shmoergh/hog/boards/ui/sheets/adsr-logic.kicad_sch

## KiCad design boards/ui/sheets/adsr-logic.kicad_sch (2025-03-16)

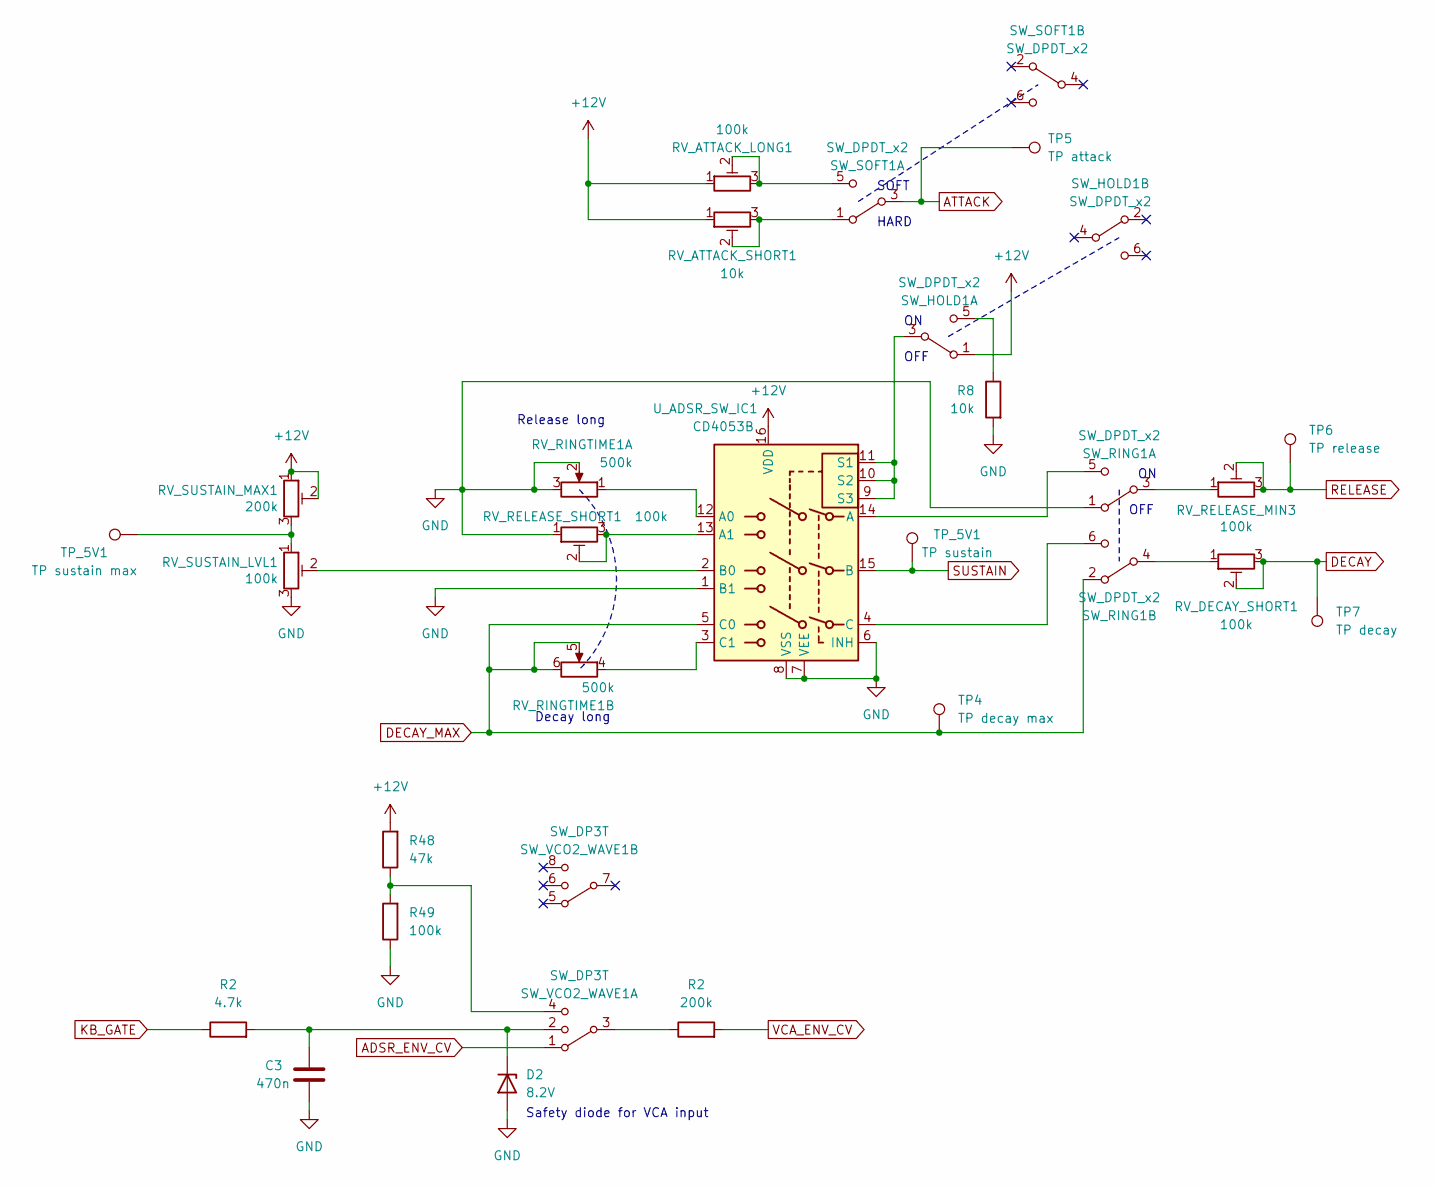
[picture p43: schematic adsr-logic.kicad_sch]

Parts:
C3: 470n; C_Disc_D3.0mm_W2.0mm_P2.50mm; Part No. 80-C315C474K5R
D2: 8.2V; D_DO-41_SOD81_P7.62mm_Horizontal; Part No. 625-BZX85C8V2
R2: 200k; R_Axial_DIN0207_L6.3mm_D2.5mm_P7.62mm_Horizontal; Part No. 603-MFR-25FTF52-200K
R8: 10k; R_Axial_DIN0207_L6.3mm_D2.5mm_P7.62mm_Horizontal; Part No. 603-MFR25SFRF52-10K
R48: 47k; R_Axial_DIN0207_L6.3mm_D2.5mm_P7.62mm_Horizontal; Part No. 603-MFR-25FTE52-47K
R49: 100k; R_Axial_DIN0207_L6.3mm_D2.5mm_P7.62mm_Horizontal; Part No. 603-MFR-25FRF52100K
RV_ATTACK_LONG1: 100k; Potentiometer_Runtron_RM-065_Vertical; Part No. 652-3306F-1-104
RV_ATTACK_SHORT1: 10k; Potentiometer_Runtron_RM-065_Vertical; Part No. 652-3306F-1-103
RV_DECAY_SHORT1: 100k; Potentiometer_Runtron_RM-065_Vertical; Part No. 652-3306F-1-104
RV_RELEASE_MIN3: 100k; Potentiometer_Runtron_RM-065_Vertical; Part No. 652-3306F-1-104
RV_RELEASE_SHORT1: 100k; Potentiometer_Runtron_RM-065_Vertical; Part No. 652-3306F-1-104
RV_RINGTIME1: 500k; Potentiometer_Bourns_Dual-PTV112-4; Part No. 652-PTV1124420AA504
RV_SUSTAIN_LVL1: 100k; Potentiometer_Runtron_RM-065_Vertical; Part No. 652-3306F-1-104
RV_SUSTAIN_MAX1: 200k; Potentiometer_Runtron_RM-065_Vertical; Part No. 652-3306F-1-204
SW_HOLD1: SW_DPDT_x2; DPDT Korg Style Switch; Part No. TS-22E01AT15
SW_RING1: SW_DPDT_x2; DPDT Korg Style Switch; Part No. TS-22E01AT15
SW_SOFT1: SW_DPDT_x2; DPDT Korg Style Switch; Part No. TS-22E01AT15
SW_VCO2_WAVE1: SW_DP3T; DP3T Korg Style Switch; Part No. TS23-E02
TP4: TP decay max; TestPoint_THTPad_2.0x2.0mm_Drill1.0mm
TP5: TP attack; TestPoint_THTPad_2.0x2.0mm_Drill1.0mm
TP6: TP release; TestPoint_THTPad_2.0x2.0mm_Drill1.0mm
TP7: TP decay; TestPoint_THTPad_2.0x2.0mm_Drill1.0mm
TP_5V1: TP sustain; TestPoint_THTPad_2.0x2.0mm_Drill1.0mm
U_ADSR_SW_IC1: CD4053B; DIP-16_W7.62mm; Part No. 595-CD4053BE

Connections:
+12V: R48.2, RV_ATTACK_LONG1.1, RV_ATTACK_SHORT1.1, RV_SUSTAIN_MAX1.1, RV_SUSTAIN_MAX1.2, SW_HOLD1.1 (A), U_ADSR_SW_IC1.16 (VDD)
ADSR_ENV_CV: SW_VCO2_WAVE1.1
ATTACK: SW_SOFT1.3 (B), TP5.1
DECAY: RV_DECAY_SHORT1.2, RV_DECAY_SHORT1.3, TP7.1
DECAY_MAX: RV_RINGTIME1.5, RV_RINGTIME1.6, SW_RING1.2 (A), TP4.1, U_ADSR_SW_IC1.5 (C0)
GND: C3.2, D2.2 (A), R8.2, R49.1, RV_RELEASE_SHORT1.1, RV_RINGTIME1.2, RV_RINGTIME1.3, RV_SUSTAIN_LVL1.3, SW_RING1.1 (A), U_ADSR_SW_IC1.1 (B1), U_ADSR_SW_IC1.6 (INH), U_ADSR_SW_IC1.7 (VEE), U_ADSR_SW_IC1.8 (VSS)
KB_GATE: R2.1
unnamed: C3.1, D2.1 (K), R2.2, SW_VCO2_WAVE1.2
unnamed: R2.1, SW_VCO2_WAVE1.3
unnamed: R8.1, SW_HOLD1.5 (C)
unnamed: R48.1, R49.2, SW_VCO2_WAVE1.4
unnamed: RV_ATTACK_LONG1.2, RV_ATTACK_LONG1.3, SW_SOFT1.5 (C)
unnamed: RV_ATTACK_SHORT1.2, RV_ATTACK_SHORT1.3, SW_SOFT1.1 (A)
unnamed: RV_DECAY_SHORT1.1, SW_RING1.4 (B)
unnamed: RV_RELEASE_MIN3.1, SW_RING1.3 (B)
unnamed: RV_RELEASE_SHORT1.2, RV_RELEASE_SHORT1.3, U_ADSR_SW_IC1.13 (A1)
unnamed: RV_RINGTIME1.1, U_ADSR_SW_IC1.12 (A0)
unnamed: RV_RINGTIME1.4, U_ADSR_SW_IC1.3 (C1)
unnamed: RV_SUSTAIN_LVL1.1, RV_SUSTAIN_MAX1.3, TP_5V1.1
unnamed: RV_SUSTAIN_LVL1.2, U_ADSR_SW_IC1.2 (B0)
unnamed: SW_HOLD1.3 (B), U_ADSR_SW_IC1.9 (S3), U_ADSR_SW_IC1.10 (S2), U_ADSR_SW_IC1.11 (S1)
unnamed: SW_RING1.5 (C), U_ADSR_SW_IC1.14 (A)
unnamed: SW_RING1.6 (C), U_ADSR_SW_IC1.4 (C)
RELEASE: RV_RELEASE_MIN3.2, RV_RELEASE_MIN3.3, TP6.1
SUSTAIN: TP_5V1.1, U_ADSR_SW_IC1.15 (B)
VCA_ENV_CV: R2.2

Notes on the sheet:
Release long
HARD
SOFT
OFF
Decay long
Safety diode for VCA input
