shmoergh/hog/boards/ui/sheets/filter_ui.kicad_sch

## KiCad design boards/ui/sheets/filter_ui.kicad_sch (2025-03-16)

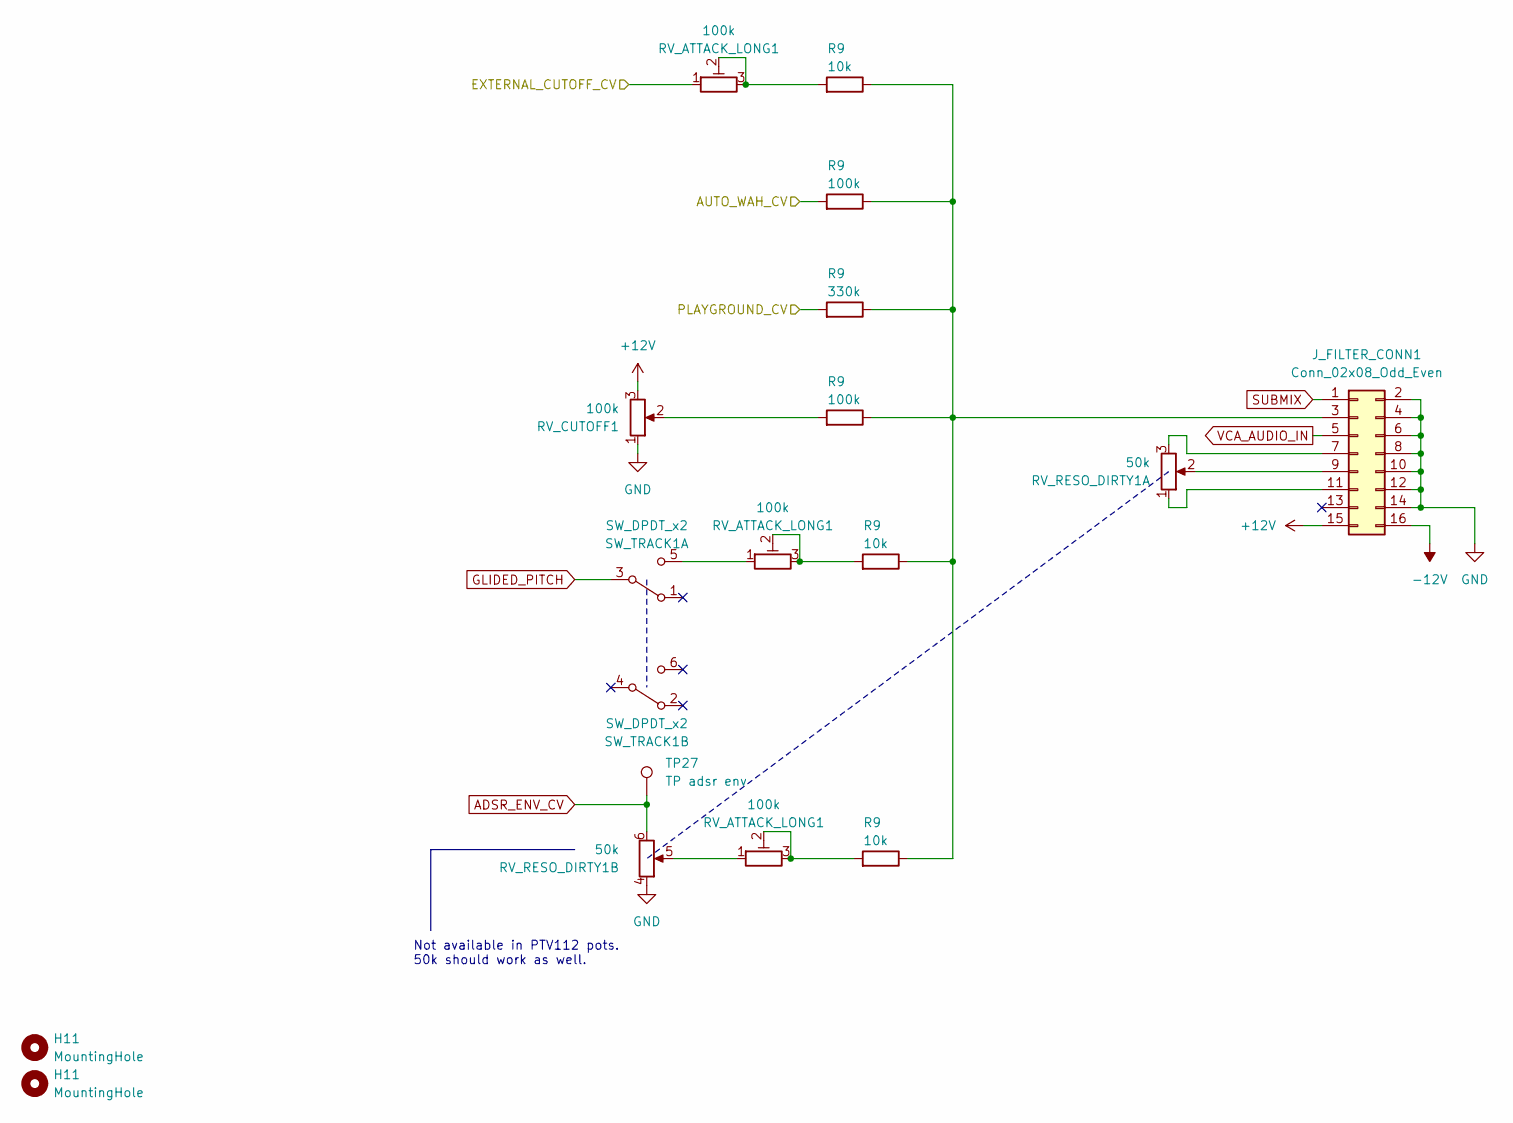
[picture p44: schematic filter_ui.kicad_sch]

Parts:
H11: MountingHole; MountingHole_3mm
J_FILTER_CONN1: Conn_02x08_Odd_Even; PinHeader_2x08_P2.54mm_Vertical; Part No. 649-1012938191601BLF
R9: 100k; R_Axial_DIN0207_L6.3mm_D2.5mm_P7.62mm_Horizontal; Part No. 603-MFR-25FRF52100K
RV_ATTACK_LONG1: 100k; Potentiometer_Runtron_RM-065_Vertical; Part No. 652-3306F-1-104
RV_CUTOFF1: 100k; Potentiometer_Bourns_Single-PTV09A; Part No. 652-PTV09A4025FB104
RV_RESO_DIRTY1: 50k; Potentiometer_Bourns_Dual-PTV112-4; Part No. 652-PTV112-4425AB503
SW_TRACK1: SW_DPDT_x2; DPDT Korg Style Switch; Part No. TS-22E01AT15
TP27: TP adsr env; TestPoint_THTPad_2.0x2.0mm_Drill1.0mm

Connections:
+12V: J_FILTER_CONN1.15, RV_CUTOFF1.3
-12V: J_FILTER_CONN1.16
ADSR_ENV_CV: RV_RESO_DIRTY1.6, TP27.1
AUTO_WAH_CV: R9.2
EXTERNAL_CUTOFF_CV: RV_ATTACK_LONG1.1
GLIDED_PITCH: SW_TRACK1.3 (B)
GND: J_FILTER_CONN1.2, J_FILTER_CONN1.4, J_FILTER_CONN1.6, J_FILTER_CONN1.8, J_FILTER_CONN1.10, J_FILTER_CONN1.12, J_FILTER_CONN1.14, RV_CUTOFF1.1, RV_RESO_DIRTY1.4
unnamed: J_FILTER_CONN1.3, R9.1
unnamed: J_FILTER_CONN1.7, RV_RESO_DIRTY1.3
unnamed: J_FILTER_CONN1.9, RV_RESO_DIRTY1.2
unnamed: J_FILTER_CONN1.11, RV_RESO_DIRTY1.1
unnamed: R9.2, RV_ATTACK_LONG1.2, RV_ATTACK_LONG1.3, RV_CUTOFF1.2
unnamed: RV_ATTACK_LONG1.1, RV_RESO_DIRTY1.5, SW_TRACK1.5 (C)
PLAYGROUND_CV: R9.2
SUBMIX: J_FILTER_CONN1.1
VCA_AUDIO_IN: J_FILTER_CONN1.5

Notes on the sheet:
Not available in PTV112 pots. 50k should work as well.
