shmoergh/hog/boards/ui/sheets/glide_ui.kicad_sch

## KiCad design boards/ui/sheets/glide_ui.kicad_sch (2024-12-14)

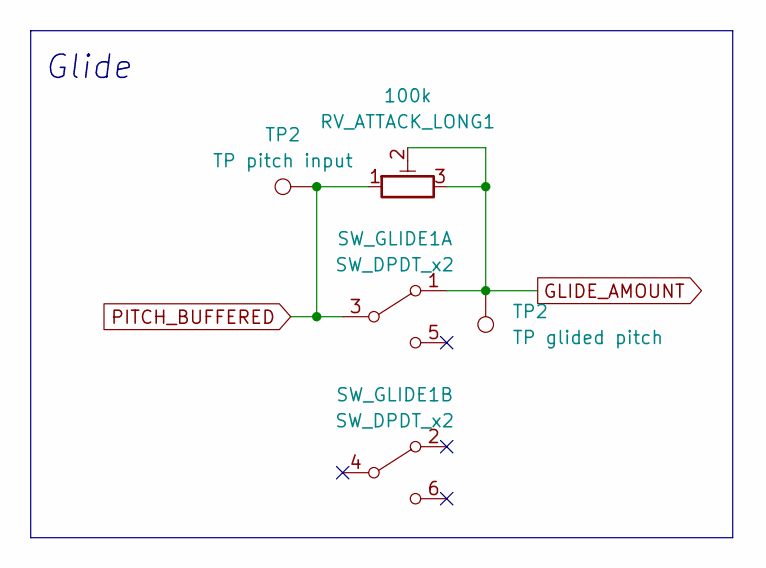
[picture p45: schematic glide_ui.kicad_sch]

Parts:
RV_ATTACK_LONG1: 100k; Potentiometer_Runtron_RM-065_Vertical; Part No. 652-3306F-1-104
SW_GLIDE1: SW_DPDT_x2; DPDT Korg Style Switch; Part No. TS-22E01AT15
TP2: TP glided pitch; TestPoint_THTPad_2.0x2.0mm_Drill1.0mm

Connections:
GLIDE_AMOUNT: RV_ATTACK_LONG1.2, RV_ATTACK_LONG1.3, SW_GLIDE1.1 (A), TP2.1
PITCH_BUFFERED: RV_ATTACK_LONG1.1, SW_GLIDE1.3 (B), TP2.1

Notes on the sheet:
Glide
