shmoergh/hog/boards/ui/sheets/io.kicad_sch

## KiCad design boards/ui/sheets/io.kicad_sch (2025-03-16)

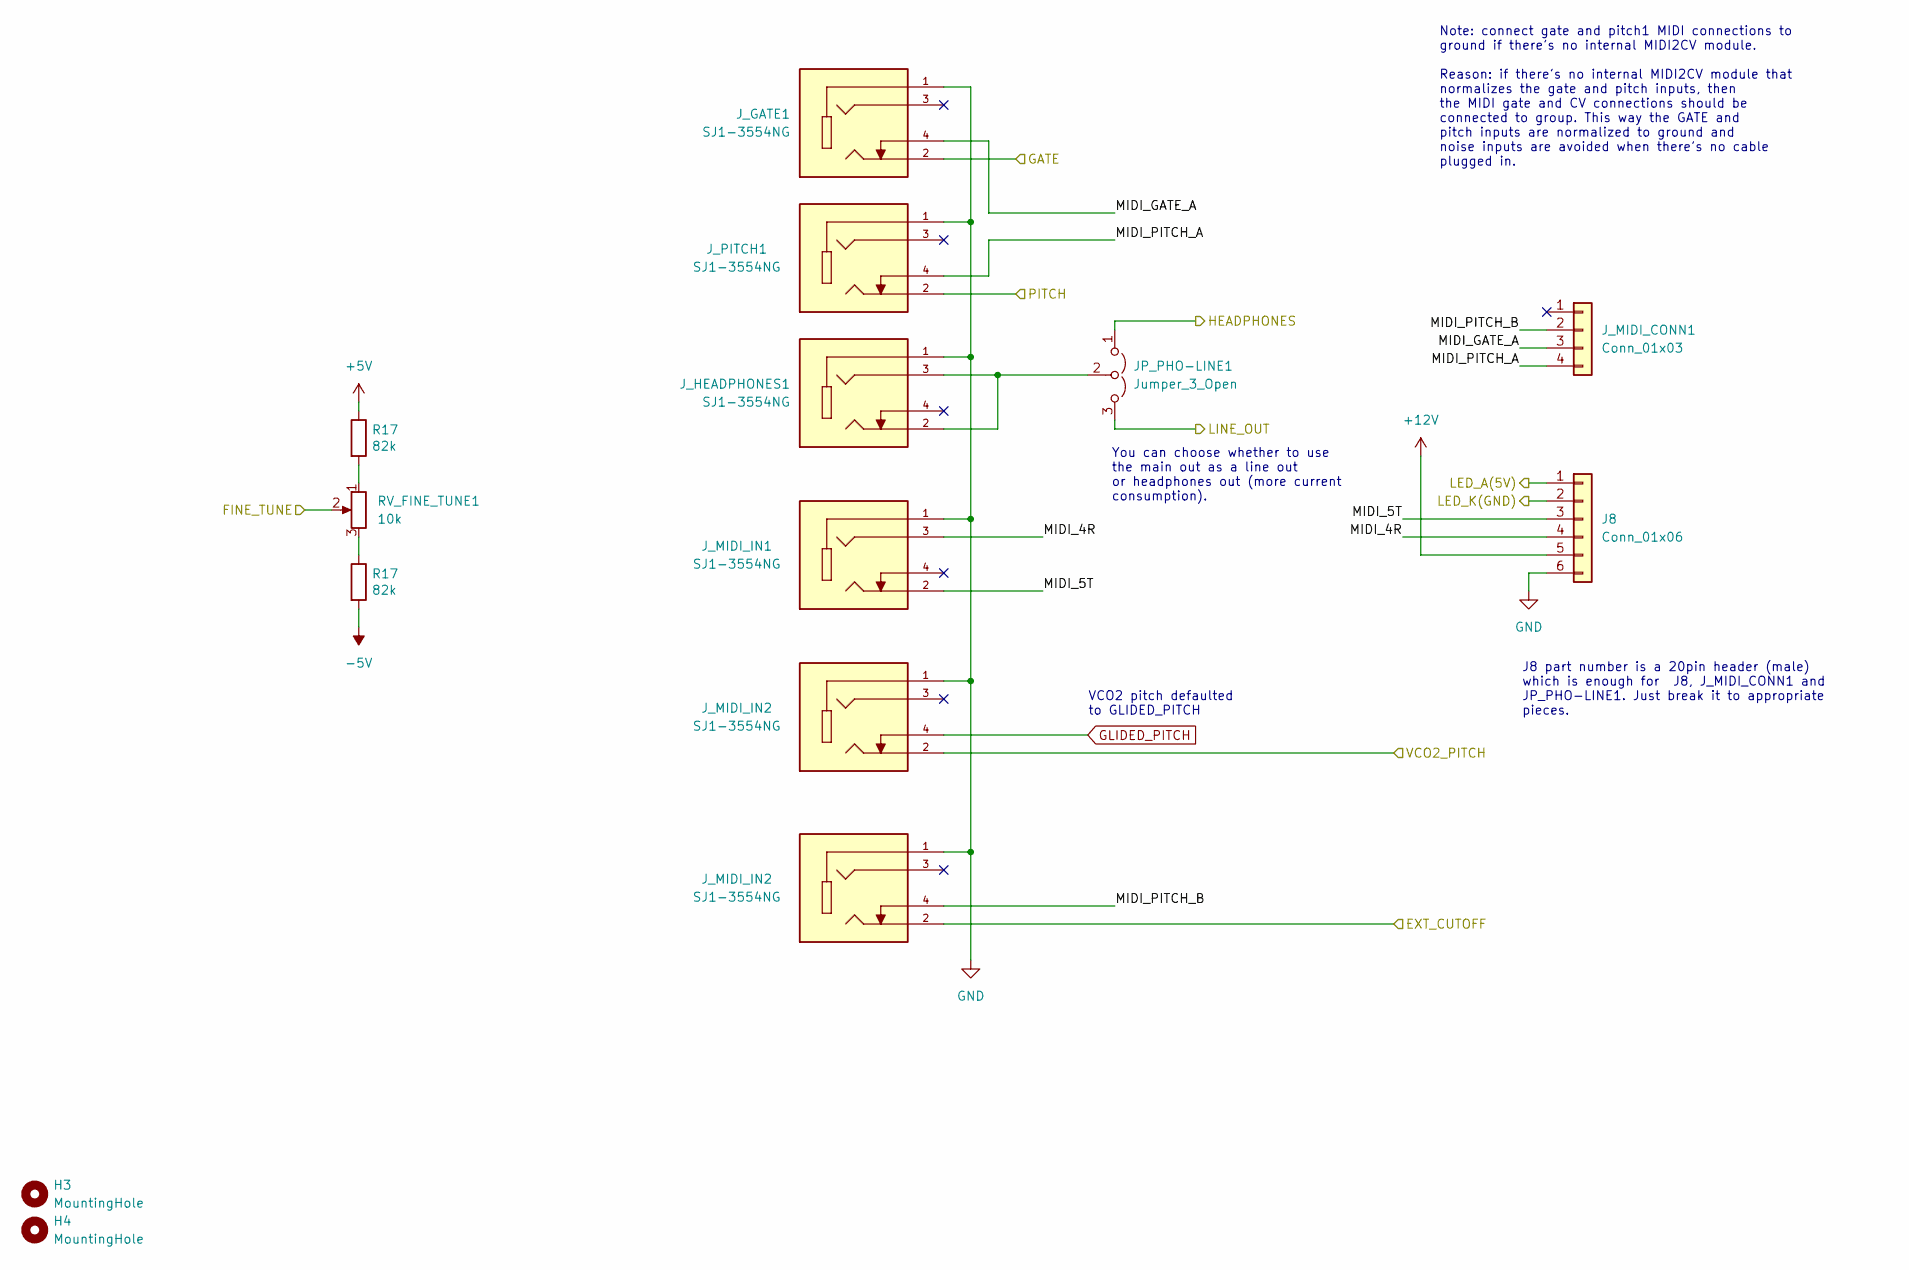
[picture p46: schematic io.kicad_sch]

Parts:
H3, H4: MountingHole; MountingHole_3mm_Pad
J8: Conn_01x06; PinHeader_1x06_P2.54mm_Vertical; Part No. 737-PH1-20-UA
JP_PHO-LINE1: Jumper_3_Open; PinHeader_1x03_P2.54mm_Vertical
J_GATE1: SJ1-3554NG; CUI_SJ1-3554NG; PARTREV 1.05
J_HEADPHONES1: SJ1-3554NG; CUI_SJ1-3554NG; PARTREV 1.05
J_MIDI_CONN1: Conn_01x03; PinHeader_1x04_P2.54mm_Vertical
J_MIDI_IN1, J_MIDI_IN2: SJ1-3554NG; CUI_SJ1-3554NG; PARTREV 1.05
J_PITCH1: SJ1-3554NG; CUI_SJ1-3554NG; PARTREV 1.05
R17: 82k; R_Axial_DIN0207_L6.3mm_D2.5mm_P7.62mm_Horizontal; Part No. 603-MFR-25FBF52-82K
RV_FINE_TUNE1: 10k; Potentiometer_Bourns_PTD901-2015_Single_Horizontal; Part No. PTD901-1015K-B103

Connections:
+5V: R17.1
+12V: J8.5
-5V: R17.2
EXT_CUTOFF: J_MIDI_IN2.2
FINE_TUNE: RV_FINE_TUNE1.2
GATE: J_GATE1.2
GLIDED_PITCH: J_MIDI_IN2.4
GND: J8.6, J_GATE1.1, J_HEADPHONES1.1, J_MIDI_IN1.1, J_MIDI_IN2.1, J_PITCH1.1
HEADPHONES: JP_PHO-LINE1.1 (A)
LED_A(5V): J8.1
LED_K(GND): J8.2
LINE_OUT: JP_PHO-LINE1.3 (B)
MIDI_4R: J8.4, J_MIDI_IN1.3
MIDI_5T: J8.3, J_MIDI_IN1.2
MIDI_GATE_A: J_GATE1.4, J_MIDI_CONN1.3
MIDI_PITCH_A: J_MIDI_CONN1.4, J_PITCH1.4
MIDI_PITCH_B: J_MIDI_CONN1.2, J_MIDI_IN2.4
unnamed: JP_PHO-LINE1.2 (C), J_HEADPHONES1.2, J_HEADPHONES1.3
unnamed: R17.1, RV_FINE_TUNE1.3
unnamed: R17.2, RV_FINE_TUNE1.1
PITCH: J_PITCH1.2
VCO2_PITCH: J_MIDI_IN2.2

Notes on the sheet:
You can choose whether to use the main out as a line out or headphones out (more current consumption).
VCO2 pitch defaulted to GLIDED_PITCH
J8 part number is a 20pin header (male) which is enough for J8, J_MIDI_CONN1 and JP_PHO-LINE1. Just break it to appropriate pieces.
Note: connect gate and pitch1 MIDI connections to ground if there's no internal MIDI2CV module. Reason: if there's no internal MIDI2CV module that normalizes the gate and pitch inputs, then the MIDI gate and CV connections should be connected to group. This way the GATE and pitch inputs are normali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
