shmoergh/hog/boards/ui/sheets/lfo_ui.kicad_sch

## KiCad design boards/ui/sheets/lfo_ui.kicad_sch (2025-03-16)

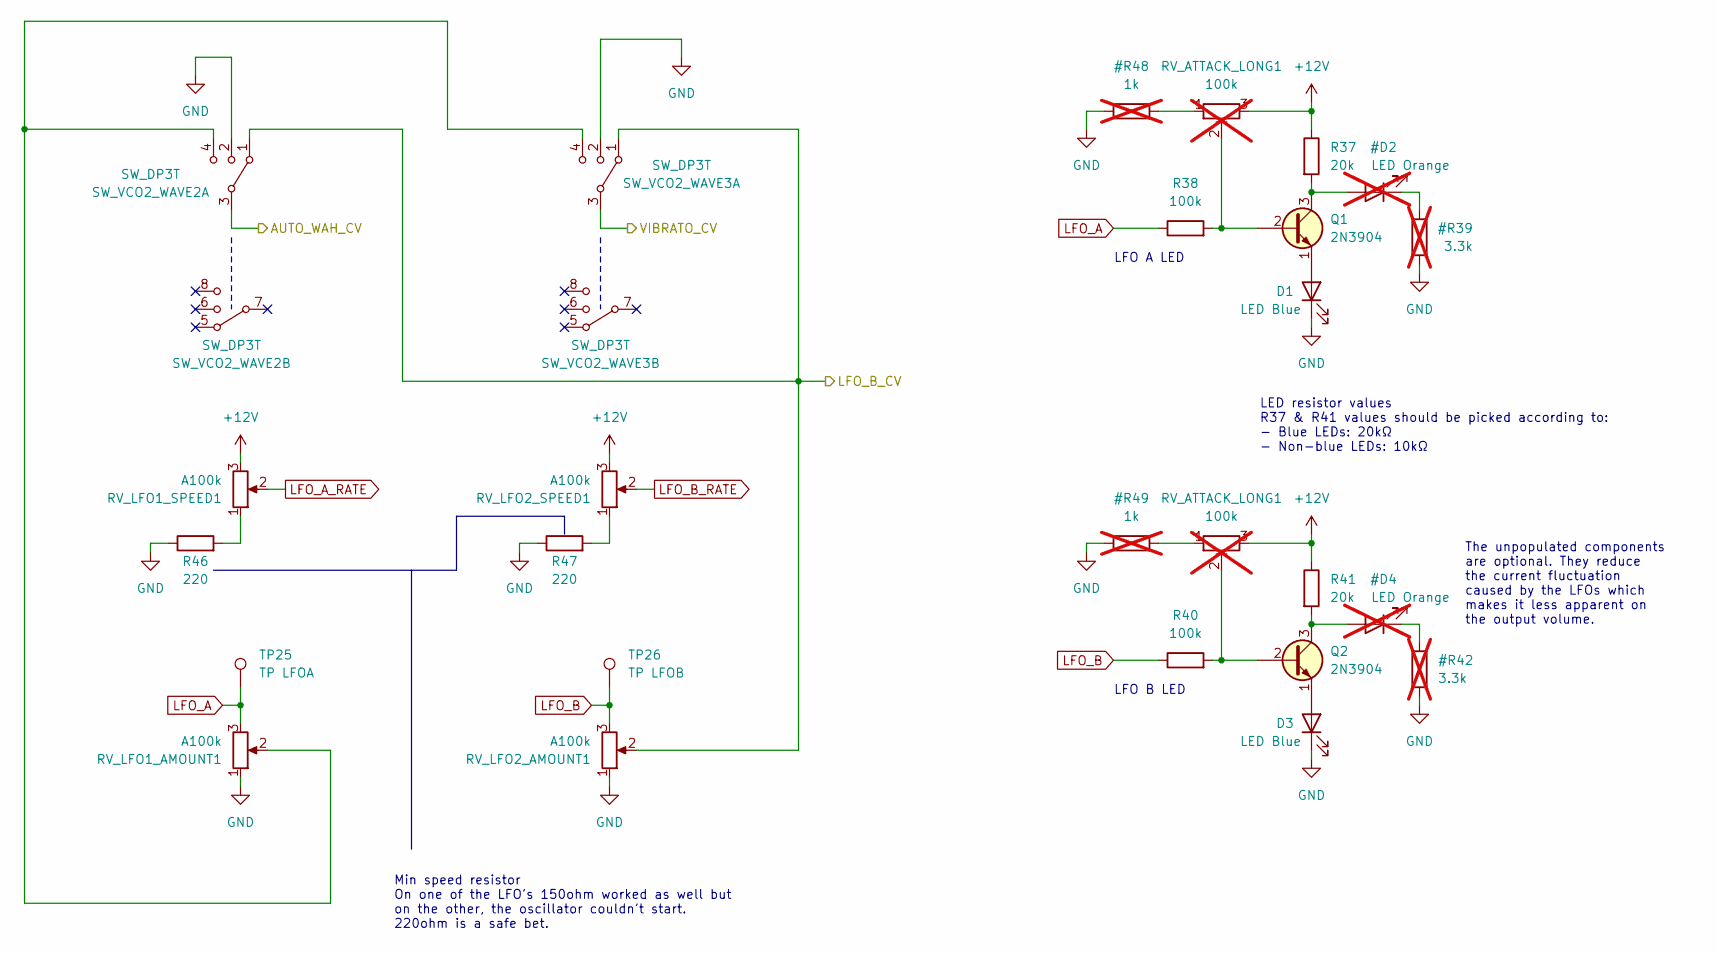
[picture p47: schematic lfo_ui.kicad_sch]

Parts:
D1, D3: LED Blue; LED_D5.0mm; Part No. 859-LTL-1CHG
Q1, Q2: 2N3904; TO-92L_Inline_Wide; Part No. 637-2N3904
R37, R41: 20k; R_Axial_DIN0207_L6.3mm_D2.5mm_P7.62mm_Horizontal; Part No. 603-MFR-25FRF5220K
R38, R40: 100k; R_Axial_DIN0207_L6.3mm_D2.5mm_P7.62mm_Horizontal; Part No. 603-MFR-25FRF52100K
R46, R47: 220; R_Axial_DIN0207_L6.3mm_D2.5mm_P7.62mm_Horizontal; Part No. 603-MFR-25FTE52-220R
RV_ATTACK_LONG1: 100k; Potentiometer_Runtron_RM-065_Vertical; Part No. 652-3306F-1-104; not fitted
RV_LFO1_AMOUNT1, RV_LFO1_SPEED1, RV_LFO2_AMOUNT1, RV_LFO2_SPEED1: A100k; Potentiometer_Bourns_Single-PTV09A; Part No. 652-PTV09A-4025UA104
SW_VCO2_WAVE2, SW_VCO2_WAVE3: SW_DP3T; DP3T Korg Style Switch; Part No. TS23-E02
TP25: TP LFOA; TestPoint_THTPad_2.0x2.0mm_Drill1.0mm
TP26: TP LFOB; TestPoint_THTPad_2.0x2.0mm_Drill1.0mm

Connections:
1k: D1.1 (K), D3.1 (K), Q1.3 (C), Q2.3 (C), R37.2, R41.2, R46.1, R47.1, RV_ATTACK_LONG1.1, RV_LFO1_AMOUNT1.1, RV_LFO2_AMOUNT1.1, SW_VCO2_WAVE2.2, SW_VCO2_WAVE3.2
+12V: R37.1, R41.1, RV_ATTACK_LONG1.3, RV_LFO1_SPEED1.3, RV_LFO2_SPEED1.3
AUTO_WAH_CV: SW_VCO2_WAVE2.3
LFO_A: R38.1, RV_LFO1_AMOUNT1.3, TP25.1
LFO_A_RATE: RV_LFO1_SPEED1.2
LFO_B: R40.1, RV_LFO2_AMOUNT1.3, TP26.1
LFO_B_CV: RV_LFO2_AMOUNT1.2, SW_VCO2_WAVE2.1, SW_VCO2_WAVE3.1
LFO_B_RATE: RV_LFO2_SPEED1.2
unnamed: D1.2 (A), Q1.1 (E)
unnamed: D3.2 (A), Q2.1 (E)
unnamed: Q1.2 (B), R38.2, RV_ATTACK_LONG1.2
unnamed: Q2.2 (B), R40.2, RV_ATTACK_LONG1.2
unnamed: R46.2, RV_LFO1_SPEED1.1
unnamed: R47.2, RV_LFO2_SPEED1.1
unnamed: RV_LFO1_AMOUNT1.2, SW_VCO2_WAVE2.4, SW_VCO2_WAVE3.4
VIBRATO_CV: SW_VCO2_WAVE3.3

Notes on the sheet:
LFO A LED
The unpopulated components are optional. They reduce the current fluctuation caused by the LFOs which makes it less apparent on the output volume.
LED resistor values R37 & R41 values should be picked according to: - Blue LEDs: 20kΩ - Non-blue LEDs: 10kΩ
Min speed resistor On one of the LFO's 150ohm worked as well but on the other, the oscillator couldn't start. 220ohm is a safe bet.
LFO B LED
