shmoergh/hog/boards/ui/sheets/main_vol_ui.kicad_sch

## KiCad design boards/ui/sheets/main_vol_ui.kicad_sch (2025-03-16)

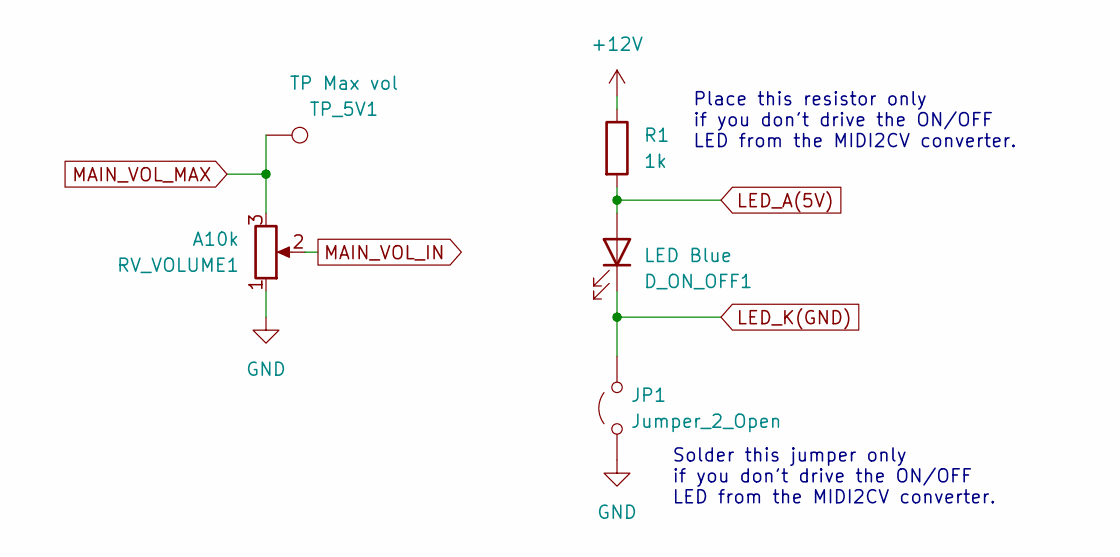
[picture p48: schematic main_vol_ui.kicad_sch]

Parts:
D_ON_OFF1: LED Blue; LED_D5.0mm; Part No. 859-LTL-1CHG
JP1: Jumper_2_Open; SolderJumper-2_P1.3mm_Bridged_Pad1.0x1.5mm
R1: 1k; R_Axial_DIN0207_L6.3mm_D2.5mm_P7.62mm_Horizontal; Part No. 603-MFR-25FBF52-1K
RV_VOLUME1: A10k; Potentiometer_Bourns_Single-PTV09A; Part No. 652-PTV09A4025FA103
TP_5V1: TP Max vol; TestPoint_THTPad_2.0x2.0mm_Drill1.0mm

Connections:
+12V: R1.1
GND: JP1.1 (A), RV_VOLUME1.1
LED_A(5V): D_ON_OFF1.2 (A), R1.2
LED_K(GND): D_ON_OFF1.1 (K), JP1.2 (B)
MAIN_VOL_IN: RV_VOLUME1.2
MAIN_VOL_MAX: RV_VOLUME1.3, TP_5V1.1

Notes on the sheet:
Place this resistor only if you don't drive the ON/OFF LED from the MIDI2CV converter.
Solder this jumper only if you don't drive the ON/OFF LED from the MIDI2CV converter.
