shmoergh/hog/boards/ui/sheets/noise_ui.kicad_sch

## KiCad design boards/ui/sheets/noise_ui.kicad_sch (2024-12-14)

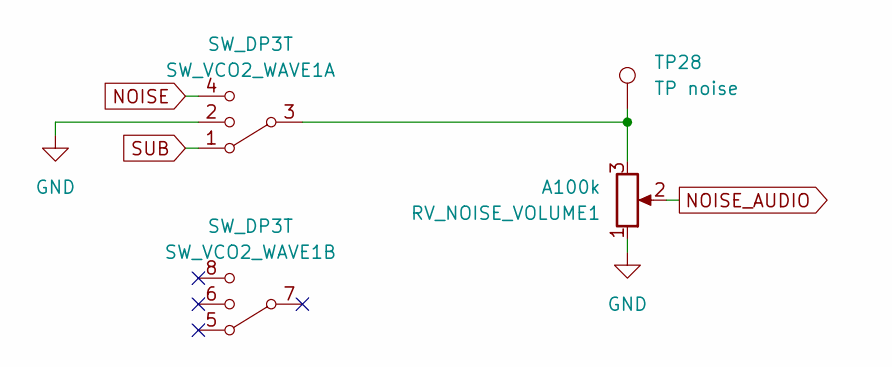
[picture p49: schematic noise_ui.kicad_sch]

Parts:
RV_NOISE_VOLUME1: A100k; Potentiometer_Bourns_Single-PTV09A; Part No. 652-PTV09A-4025UA104
SW_VCO2_WAVE1: SW_DP3T; DP3T Korg Style Switch; Part No. TS23-E02
TP28: TP noise; TestPoint_THTPad_2.0x2.0mm_Drill1.0mm

Connections:
GND: RV_NOISE_VOLUME1.1, SW_VCO2_WAVE1.2
NOISE: SW_VCO2_WAVE1.4
NOISE_AUDIO: RV_NOISE_VOLUME1.2
unnamed: RV_NOISE_VOLUME1.3, SW_VCO2_WAVE1.3, TP28.1
SUB: SW_VCO2_WAVE1.1
