shmoergh/hog/boards/ui/sheets/playground_ui.kicad_sch

## KiCad design boards/ui/sheets/playground_ui.kicad_sch (2025-03-16)

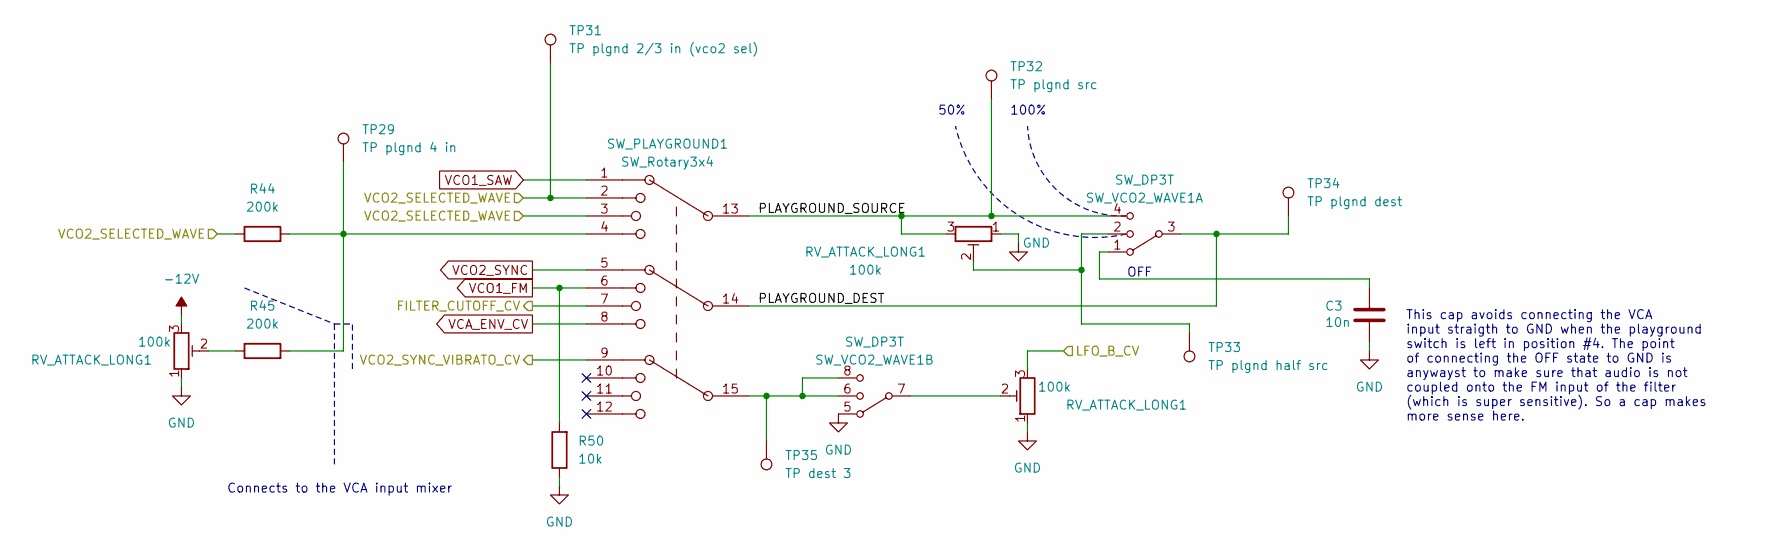
[picture p50: schematic playground_ui.kicad_sch]

Parts:
C3: 10n; C_Disc_D3.0mm_W2.0mm_P2.50mm; Part No. 594-K103K15X7RF5TK2
R44, R45: 200k; R_Axial_DIN0207_L6.3mm_D2.5mm_P7.62mm_Horizontal; Part No. 603-MFR-25FTF52-200K
R50: 10k; R_Axial_DIN0207_L6.3mm_D2.5mm_P7.62mm_Horizontal; Part No. 603-MFR25SFRF52-10K
RV_ATTACK_LONG1: 100k; Potentiometer_Runtron_RM-065_Vertical; Part No. 652-3306F-1-104
SW_PLAYGROUND1: SW_Rotary3x4; SW_SR2512F-3x4-rotary; Part No. 105-SR2512F-34NS
SW_VCO2_WAVE1: SW_DP3T; DP3T Korg Style Switch; Part No. TS23-E02
TP29: TP plgnd 4 in; TestPoint_THTPad_2.0x2.0mm_Drill1.0mm
TP31: TP plgnd 2/3 in (vco2 sel); TestPoint_THTPad_2.0x2.0mm_Drill1.0mm
TP32: TP plgnd src; TestPoint_THTPad_2.0x2.0mm_Drill1.0mm
TP33: TP plgnd half src; TestPoint_THTPad_2.0x2.0mm_Drill1.0mm
TP34: TP plgnd dest; TestPoint_THTPad_2.0x2.0mm_Drill1.0mm
TP35: TP dest 3; TestPoint_THTPad_2.0x2.0mm_Drill1.0mm

Connections:
-12V: RV_ATTACK_LONG1.3
FILTER_CUTOFF_CV: SW_PLAYGROUND1.7
GND: C3.2, R50.1, RV_ATTACK_LONG1.1, SW_VCO2_WAVE1.5
LFO_B_CV: RV_ATTACK_LONG1.3
unnamed: C3.1, SW_VCO2_WAVE1.1
unnamed: R44.2, R45.2, SW_PLAYGROUND1.4, TP29.1
unnamed: R45.1, RV_ATTACK_LONG1.2
unnamed: RV_ATTACK_LONG1.2, SW_VCO2_WAVE1.2, SW_VCO2_WAVE1.7, TP33.1
unnamed: SW_PLAYGROUND1.15, SW_VCO2_WAVE1.6, SW_VCO2_WAVE1.8, TP35.1
PLAYGROUND_DEST: SW_PLAYGROUND1.14, SW_VCO2_WAVE1.3, TP34.1
PLAYGROUND_SOURCE: RV_ATTACK_LONG1.3, SW_PLAYGROUND1.13, SW_VCO2_WAVE1.4, TP32.1
VCA_ENV_CV: SW_PLAYGROUND1.8
VCO1_FM: R50.2, SW_PLAYGROUND1.6
VCO1_SAW: SW_PLAYGROUND1.1
VCO2_SELECTED_WAVE: R44.1, SW_PLAYGROUND1.2, SW_PLAYGROUND1.3, TP31.1
VCO2_SYNC: SW_PLAYGROUND1.5
VCO2_SYNC_VIBRATO_CV: SW_PLAYGROUND1.9

Notes on the sheet:
Connects to the VCA input mixer
50%
This cap avoids connecting the VCA input straigth to GND when the playground switch is left in position #4. The point of connecting the OFF state to GND is anywayst to make sure that audio is not coupled onto the FM input of the filter (which is super sensitive). So a cap makes more sense here.
OFF
100%
