shmoergh/hog/boards/ui/sheets/power.kicad_sch

## KiCad design boards/ui/sheets/power.kicad_sch (2025-03-16)

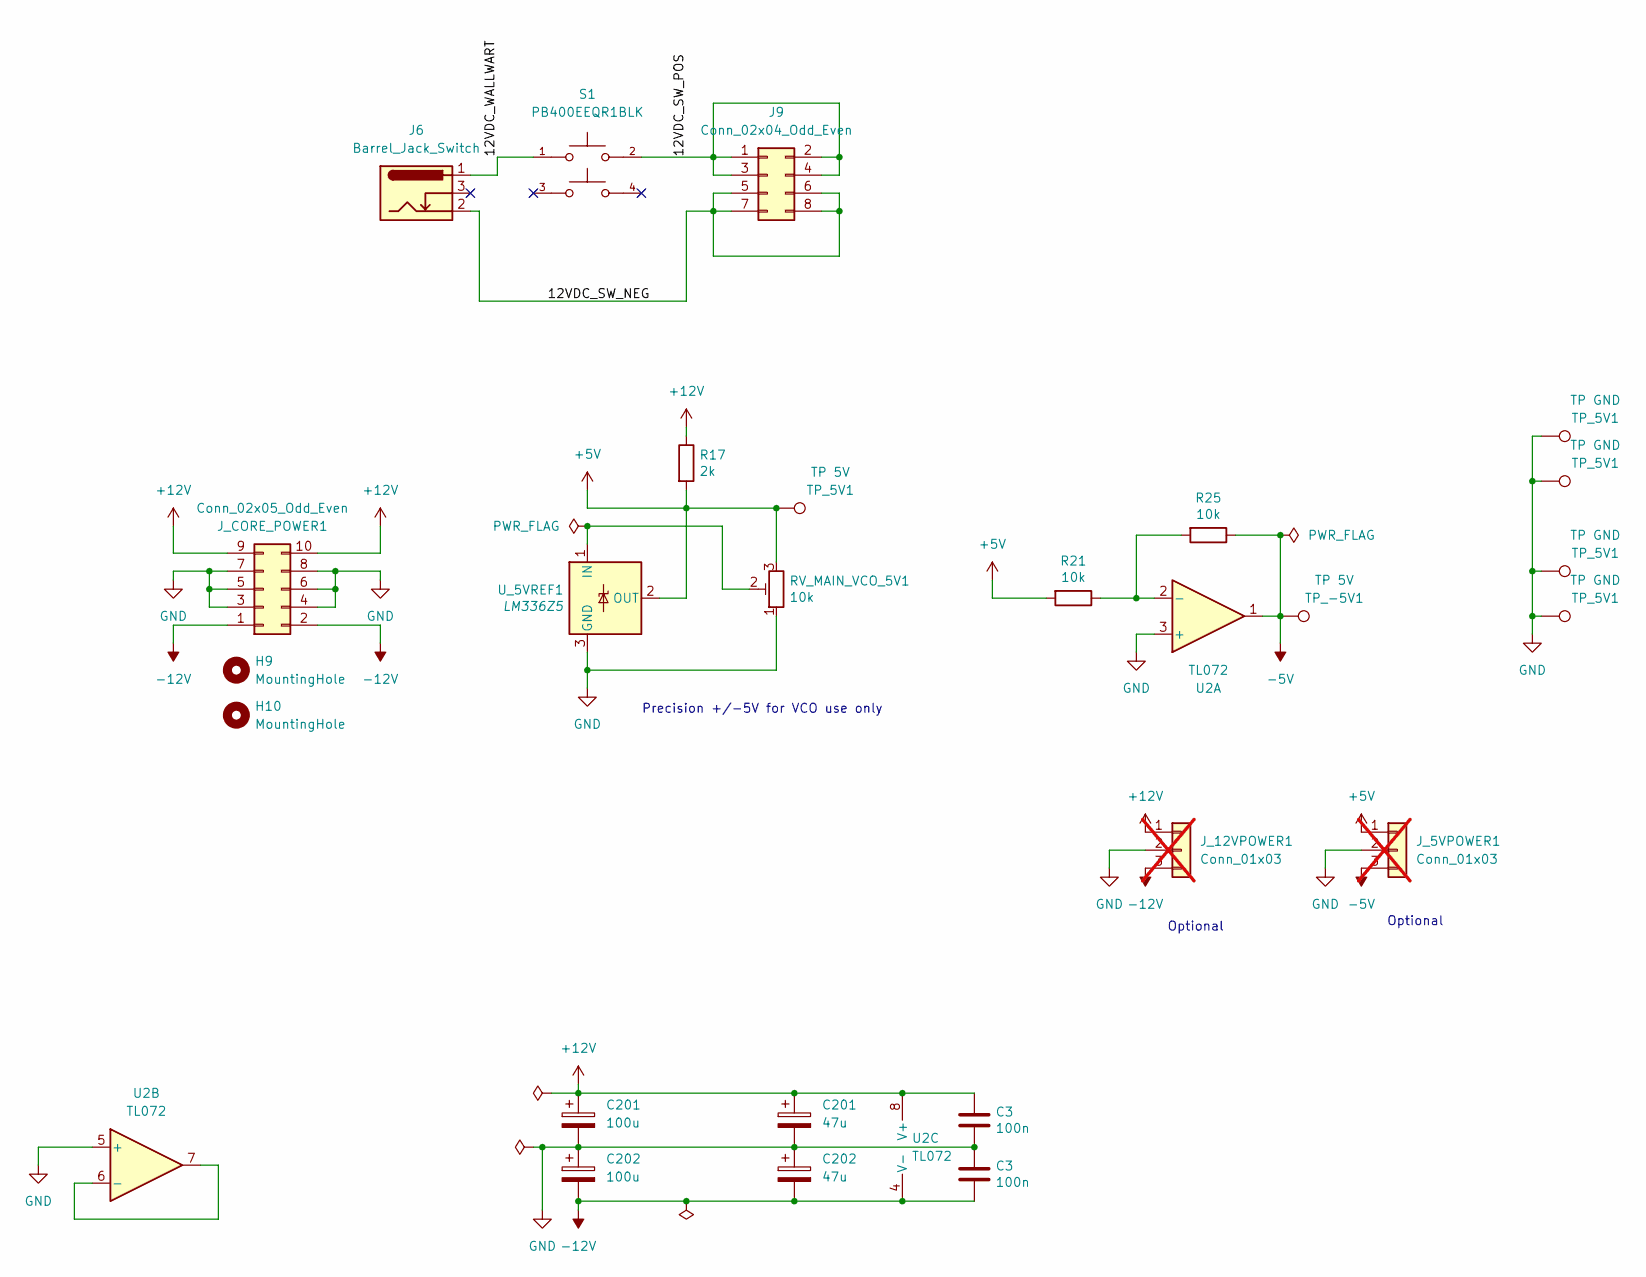
[picture p51: schematic power.kicad_sch]

Parts:
C3: 100n; C_Disc_D3.0mm_W2.0mm_P2.50mm; Part No. 594-K103K15X7RF5TK2
C201, C202: 100u; CP_Radial_D6.3mm_P2.50mm; Part No. 80-ESS107M025AE2AA
H9, H10: MountingHole; MountingHole_3mm
J6: Barrel_Jack_Switch; BarrelJack_Wuerth_6941xx301002; Part No. 710-694106301002
J9: Conn_02x04_Odd_Even; PinHeader_2x04_P2.54mm_Vertical; Part No. 737-PH2-08-UA
J_5VPOWER1, J_12VPOWER1: Conn_01x03; PinHeader_1x03_P2.54mm_Vertical; not fitted
J_CORE_POWER1: Conn_02x05_Odd_Even; PinHeader_2x05_P2.54mm_Vertical; Part No. 737-PH2-10-UA
R17: 2k; R_Axial_DIN0207_L6.3mm_D2.5mm_P7.62mm_Horizontal; Part No. 603-MFR-25FTF52-2K
R21, R25: 10k; R_Axial_DIN0207_L6.3mm_D2.5mm_P7.62mm_Horizontal; Part No. 603-MFR25SFRF52-10K
RV_MAIN_VCO_5V1: 10k; Potentiometer_Bourns_3006P_Horizontal; Part No. 652-3006P-1-103-LF
S1: PB400EEQR1BLK; SW_PB400EEQR1BLK; PARTREV A
TP_5V1: TP GND; TestPoint_THTPad_2.0x2.0mm_Drill1.0mm
TP_-5V1: TP 5V; TestPoint_THTPad_2.0x2.0mm_Drill1.0mm
U2: TL072; DIP-8_W7.62mm_Socket_LongPads; Part No. 595-TL072IP
U_5VREF1: LM336Z5; TO-92L_Inline_Wide; Part No. 926-LM336Z-50/NOPB

Connections:
12VDC_SW_NEG: J6.2, J9.5, J9.6, J9.7, J9.8
12VDC_SW_POS: J9.1, J9.2, J9.3, J9.4, S1.2
12VDC_WALLWART: J6.1, S1.1
+5V: J_5VPOWER1.1, R17.2, R21.2, RV_MAIN_VCO_5V1.3, TP_5V1.1, U_5VREF1.2 (OUT)
+12V: C3.1, C201.1, J_12VPOWER1.1, J_CORE_POWER1.9, J_CORE_POWER1.10, R17.1, U2.8 (V+)
-5V: J_5VPOWER1.3, R25.1, TP_-5V1.1, U2.1
-12V: C3.2, C202.2, J_12VPOWER1.3, J_CORE_POWER1.1, J_CORE_POWER1.2, U2.4 (V-)
GND: C3.1, C3.2, C201.2, C202.1, J_5VPOWER1.2, J_12VPOWER1.2, J_CORE_POWER1.3, J_CORE_POWER1.4, J_CORE_POWER1.5, J_CORE_POWER1.6, J_CORE_POWER1.7, J_CORE_POWER1.8, RV_MAIN_VCO_5V1.1, TP_5V1.1, U2.3 (+), U2.5 (+), U_5VREF1.3 (GND)
unnamed: R21.1, R25.2, U2.2 (-)
unnamed: RV_MAIN_VCO_5V1.2, U_5VREF1.1 (IN)
unnamed: U2.6 (-), U2.7

Notes on the sheet:
Optional
Precision +/-5V for VCO use only
