shmoergh/hog/boards/ui/sheets/vco1_ui.kicad_sch

## KiCad design boards/ui/sheets/vco1_ui.kicad_sch (2025-03-16)

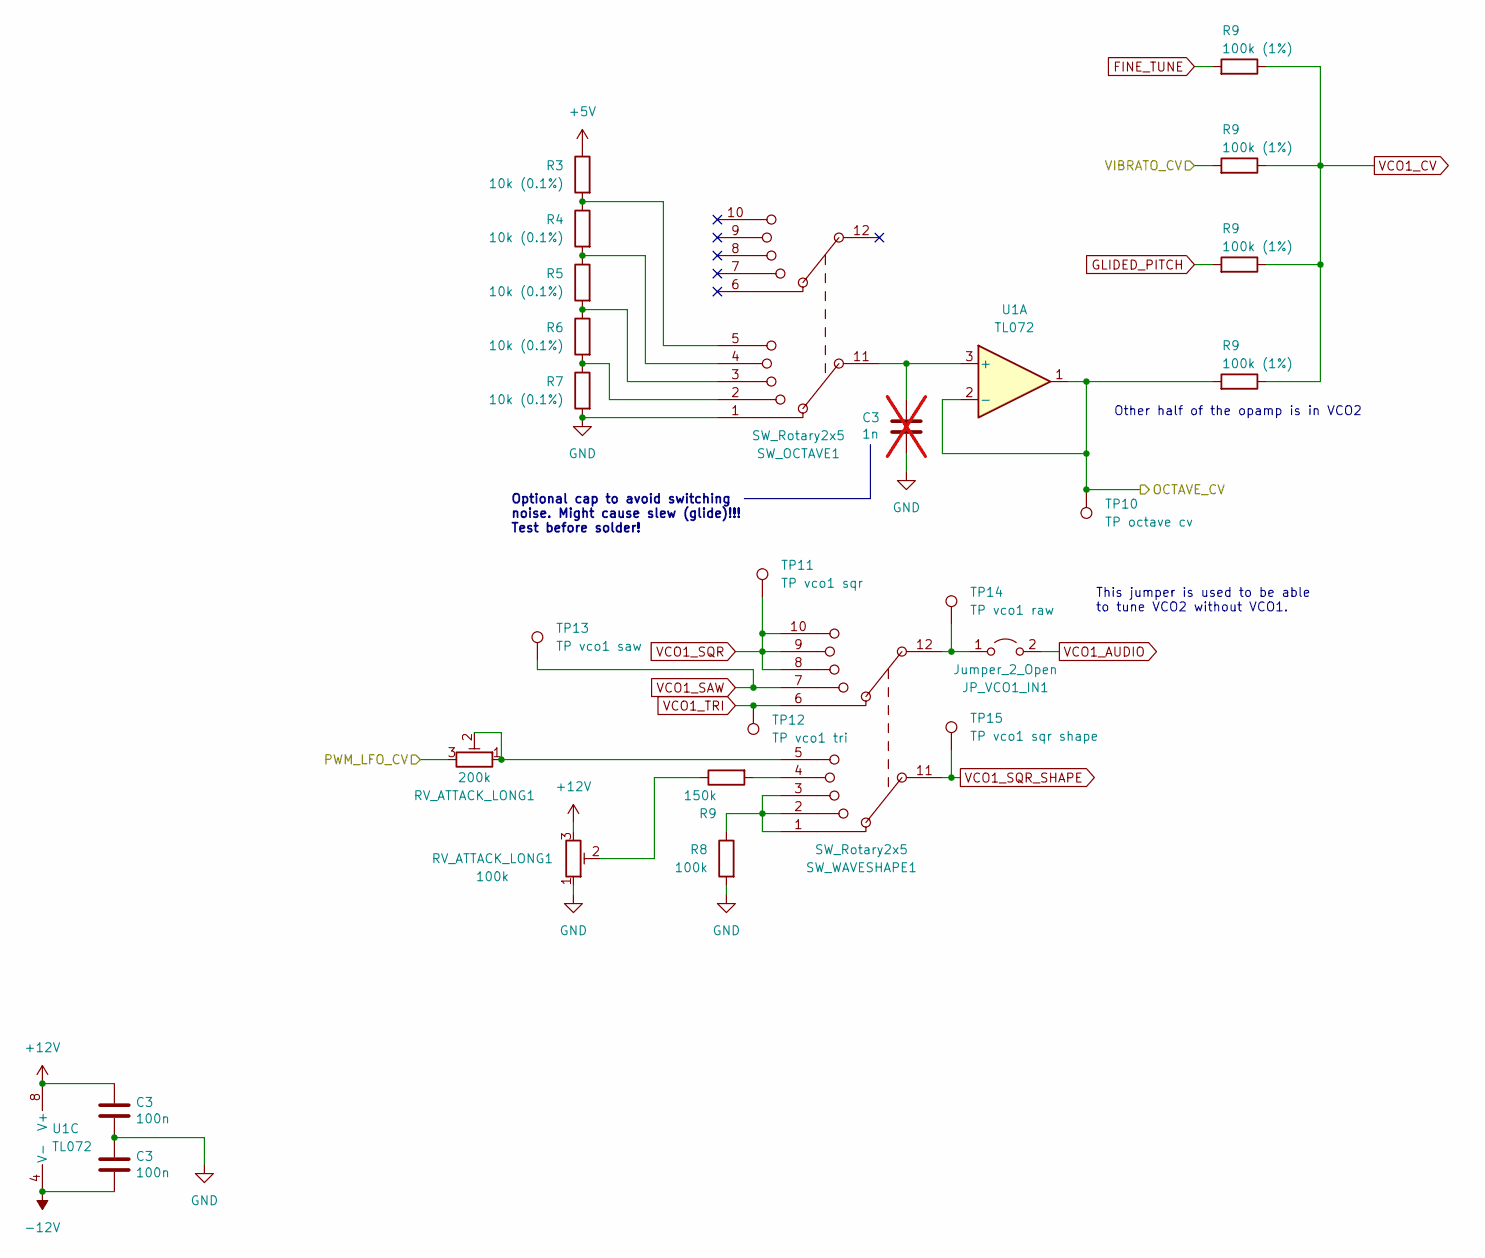
[picture p52: schematic vco1_ui.kicad_sch]

Parts:
C3: 100n; C_Disc_D3.0mm_W2.0mm_P2.50mm; Part No. 594-K103K15X7RF5TK2
JP_VCO1_IN1: Jumper_2_Open; PinHeader_1x02_P2.54mm_Vertical
R3, R4, R5, R6, R7: 10k (0.1%); R_Axial_DIN0207_L6.3mm_D2.5mm_P7.62mm_Horizontal; Part No. 660-MF1/4CCT52R1002B
R8: 100k; R_Axial_DIN0207_L6.3mm_D2.5mm_P7.62mm_Horizontal; Part No. 603-MFR-25FRF52100K
R9: 150k; R_Axial_DIN0207_L6.3mm_D2.5mm_P7.62mm_Horizontal; Part No. 603-MFR-25FBF52-150K
RV_ATTACK_LONG1: 200k; Potentiometer_Runtron_RM-065_Vertical; Part No. 652-3306F-1-204
SW_OCTAVE1: SW_Rotary2x5; SW_SR2512F-2x5-rotary; Part No. 105-SR2512F-25NS
SW_WAVESHAPE1: SW_Rotary2x5; SW_SR2512F-2x5-rotary; Part No. 105-SR2512F-25NS
TP10: TP octave cv; TestPoint_THTPad_2.0x2.0mm_Drill1.0mm
TP11: TP vco1 sqr; TestPoint_THTPad_2.0x2.0mm_Drill1.0mm
TP12: TP vco1 tri; TestPoint_THTPad_2.0x2.0mm_Drill1.0mm
TP13: TP vco1 saw; TestPoint_THTPad_2.0x2.0mm_Drill1.0mm
TP14: TP vco1 raw; TestPoint_THTPad_2.0x2.0mm_Drill1.0mm
TP15: TP vco1 sqr shape; TestPoint_THTPad_2.0x2.0mm_Drill1.0mm
U1: TL072; DIP-8_W7.62mm_Socket_LongPads; Part No. 595-TL072IP

Connections:
+5V: R3.1
+12V: C3.1, RV_ATTACK_LONG1.3, U1.8 (V+)
-12V: C3.2, U1.4 (V-)
FINE_TUNE: R9.2
GLIDED_PITCH: R9.2
GND: C3.1, C3.2, R7.2, R8.2, RV_ATTACK_LONG1.1, SW_OCTAVE1.1
unnamed: C3.1, SW_OCTAVE1.11, U1.3 (+)
unnamed: JP_VCO1_IN1.1 (A), SW_WAVESHAPE1.12, TP14.1
unnamed: R3.2, R4.1, SW_OCTAVE1.5
unnamed: R4.2, R5.1, SW_OCTAVE1.4
unnamed: R5.2, R6.1, SW_OCTAVE1.3
unnamed: R6.2, R7.1, SW_OCTAVE1.2
unnamed: R8.1, SW_WAVESHAPE1.1, SW_WAVESHAPE1.2, SW_WAVESHAPE1.3
unnamed: R9.1, RV_ATTACK_LONG1.2
unnamed: R9.2, SW_WAVESHAPE1.4
unnamed: RV_ATTACK_LONG1.1, RV_ATTACK_LONG1.2, SW_WAVESHAPE1.5
OCTAVE_CV: R9.2, TP10.1, U1.1, U1.2 (-)
PWM_LFO_CV: RV_ATTACK_LONG1.3
VCO1_AUDIO: JP_VCO1_IN1.2 (B)
VCO1_CV: R9.1
VCO1_SAW: SW_WAVESHAPE1.7, TP13.1
VCO1_SQR: SW_WAVESHAPE1.8, SW_WAVESHAPE1.9, SW_WAVESHAPE1.10, TP11.1
VCO1_SQR_SHAPE: SW_WAVESHAPE1.11, TP15.1
VCO1_TRI: SW_WAVESHAPE1.6, TP12.1
VIBRATO_CV: R9.2

Notes on the sheet:
This jumper is used to be able to tune VCO2 without VCO1.
Other half of the opamp is in VCO2
Optional cap to avoid switching noise. Might cause slew (glide)!!! Test before solder!
