shmoergh/hog/boards/ui/sheets/vco2_ui.kicad_sch

## KiCad design boards/ui/sheets/vco2_ui.kicad_sch (2025-03-16)

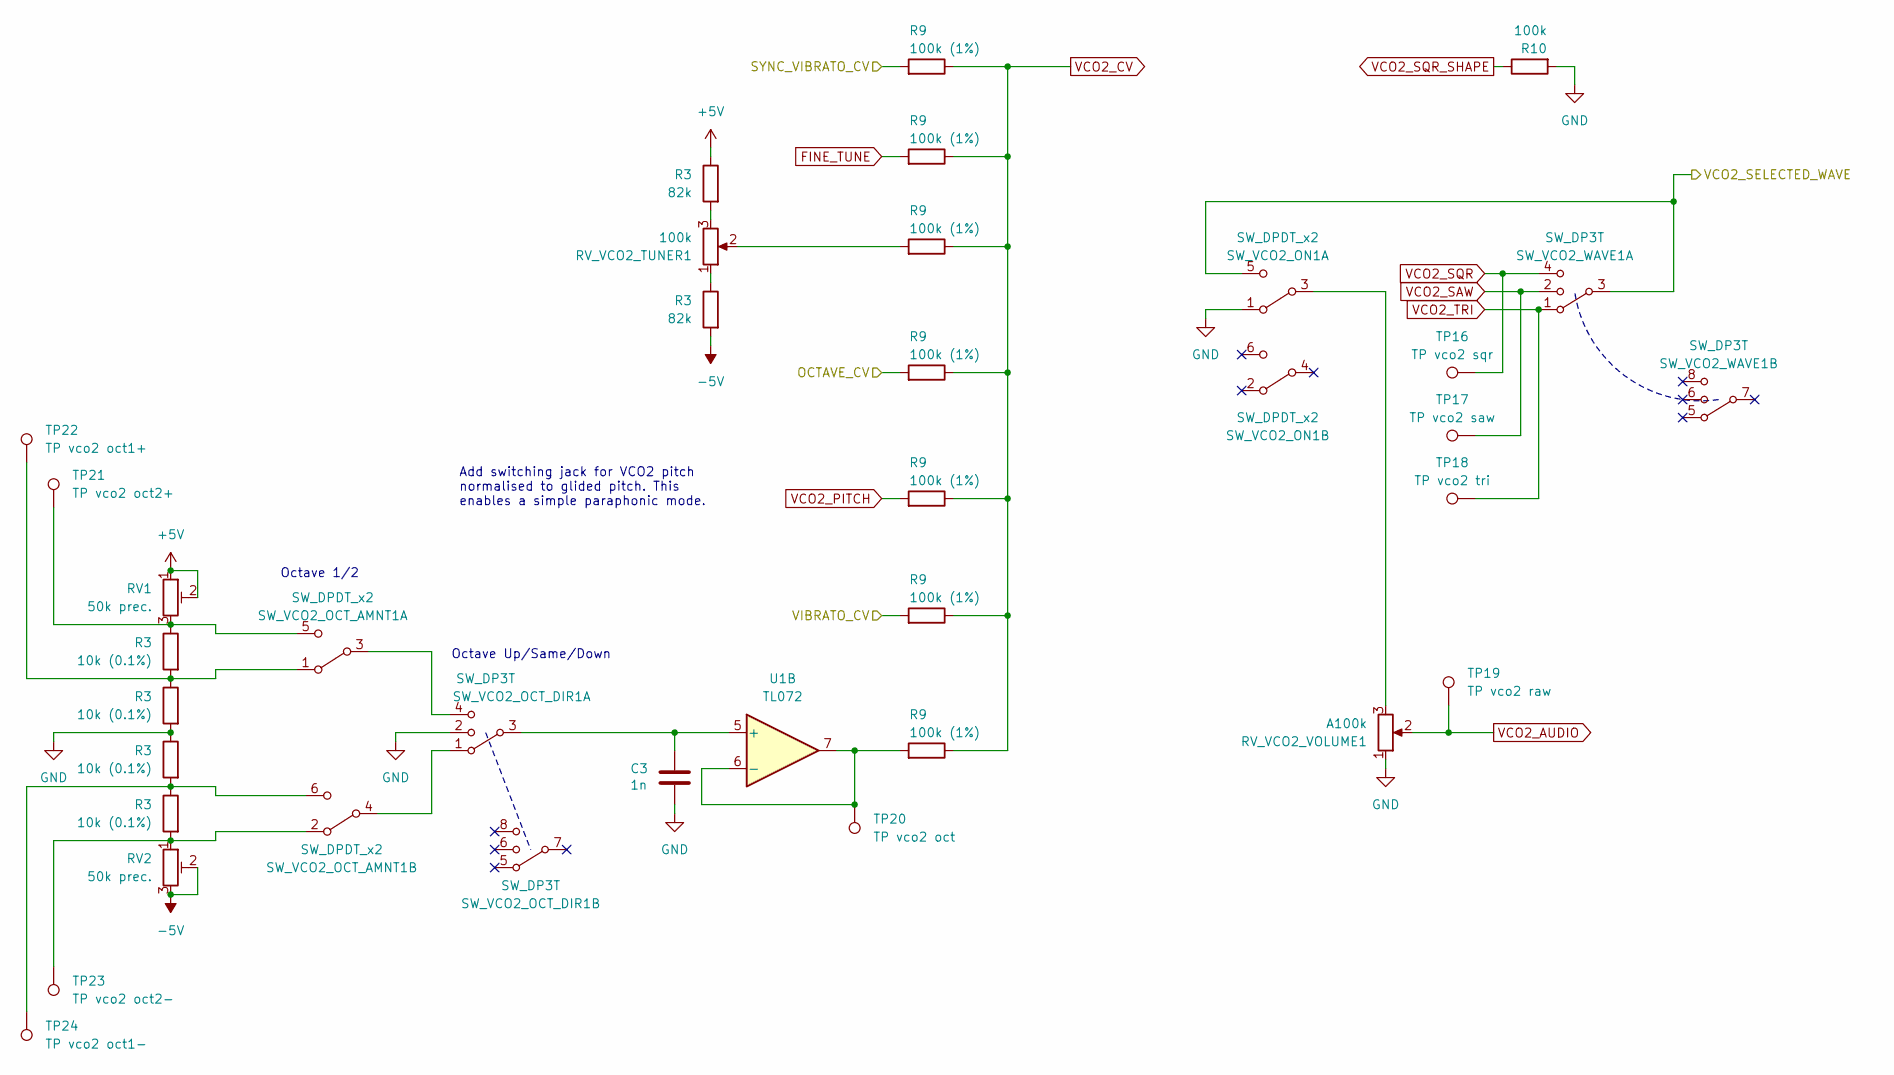
[picture p53: schematic vco2_ui.kicad_sch]

Parts:
C3: 1n; C_Disc_D3.0mm_W2.0mm_P2.50mm; Part No. 594-K102M15X7RF53L2
R3: 10k (0.1%); R_Axial_DIN0207_L6.3mm_D2.5mm_P7.62mm_Horizontal; Part No. 660-MF1/4CCT52R1002B
R9: 100k (1%); R_Axial_DIN0207_L6.3mm_D2.5mm_P7.62mm_Horizontal; Part No. 603-MFR-25FRF52100K
R10: 100k; R_Axial_DIN0207_L6.3mm_D2.5mm_P7.62mm_Horizontal; Part No. 603-MFR-25FRF52100K
RV1, RV2: 50k prec.; Potentiometer_Bourns_3006P_Horizontal; Part No. 652-3006P-1-503-LF
RV_VCO2_TUNER1: 100k; Potentiometer_Bourns_Single-PTV09A; Part No. 652-PTV09A4025FB104
RV_VCO2_VOLUME1: A100k; Potentiometer_Bourns_Single-PTV09A; Part No. 652-PTV09A-4025UA104
SW_VCO2_OCT_AMNT1, SW_VCO2_ON1: SW_DPDT_x2; DPDT Korg Style Switch; Part No. TS-22E01AT15
SW_VCO2_OCT_DIR1, SW_VCO2_WAVE1: SW_DP3T; DP3T Korg Style Switch; Part No. TS23-E02
TP16: TP vco2 sqr; TestPoint_THTPad_2.0x2.0mm_Drill1.0mm
TP17: TP vco2 saw; TestPoint_THTPad_2.0x2.0mm_Drill1.0mm
TP18: TP vco2 tri; TestPoint_THTPad_2.0x2.0mm_Drill1.0mm
TP19: TP vco2 raw; TestPoint_THTPad_2.0x2.0mm_Drill1.0mm
TP20: TP vco2 oct; TestPoint_THTPad_2.0x2.0mm_Drill1.0mm
TP21: TP vco2 oct2+; TestPoint_THTPad_2.0x2.0mm_Drill1.0mm
TP22: TP vco2 oct1+; TestPoint_THTPad_2.0x2.0mm_Drill1.0mm
TP23: TP vco2 oct2-; TestPoint_THTPad_2.0x2.0mm_Drill1.0mm
TP24: TP vco2 oct1-; TestPoint_THTPad_2.0x2.0mm_Drill1.0mm
U1: TL072; DIP-8_W7.62mm_Socket_LongPads; Part No. 595-TL072IP

Connections:
+5V: R3.1, RV1.1, RV1.2
-5V: R3.2, RV2.2, RV2.3
FINE_TUNE: R9.2
GND: C3.2, R3.1, R3.2, R10.2, RV_VCO2_VOLUME1.1, SW_VCO2_OCT_DIR1.2, SW_VCO2_ON1.1 (A)
unnamed: C3.1, SW_VCO2_OCT_DIR1.3, U1.5 (+)
unnamed: R3.1, R3.2, RV1.3, RV_VCO2_TUNER1.1, SW_VCO2_OCT_AMNT1.1 (A), SW_VCO2_OCT_AMNT1.5 (C), SW_VCO2_OCT_AMNT1.6 (C), TP21.1, TP22.1, TP24.1
unnamed: R3.2, RV2.1, RV_VCO2_TUNER1.3, SW_VCO2_OCT_AMNT1.2 (A), TP23.1
unnamed: R9.2, RV_VCO2_TUNER1.2, TP20.1, U1.6 (-), U1.7
unnamed: RV_VCO2_VOLUME1.3, SW_VCO2_ON1.3 (B)
unnamed: SW_VCO2_OCT_AMNT1.3 (B), SW_VCO2_OCT_DIR1.4
unnamed: SW_VCO2_OCT_AMNT1.4 (B), SW_VCO2_OCT_DIR1.1
OCTAVE_CV: R9.2
SYNC_VIBRATO_CV: R9.2
VCO2_AUDIO: RV_VCO2_VOLUME1.2, TP19.1
VCO2_CV: R9.1
VCO2_PITCH: R9.2
VCO2_SAW: SW_VCO2_WAVE1.2, TP17.1
VCO2_SELECTED_WAVE: SW_VCO2_ON1.5 (C), SW_VCO2_WAVE1.3
VCO2_SQR: SW_VCO2_WAVE1.4, TP16.1
VCO2_SQR_SHAPE: R10.1
VCO2_TRI: SW_VCO2_WAVE1.1, TP18.1
VIBRATO_CV: R9.2

Notes on the sheet:
Octave Up/Same/Down
Add switching jack for VCO2 pitch normalised to glided pitch. This enables a simple paraphonic mode.
Octave 1/2
